chubbyginger/ESP8266Watch/ESP8266Watch/ButtonEvents.ino

void btnleftClickedFunc() {
  btnleftClicked = true;
}

void btnenterClickedFunc() {
  btnenterClicked = true;
}

void btnrightClickedFunc() {
  btnrightClicked = true;
}

void btnbackClickedFunc() {
  btnbackClicked = true;
}
